InteliProjects/2023M4T7Inteli-grupo2/document/outros/imagens/cincoforcas2 (1).png

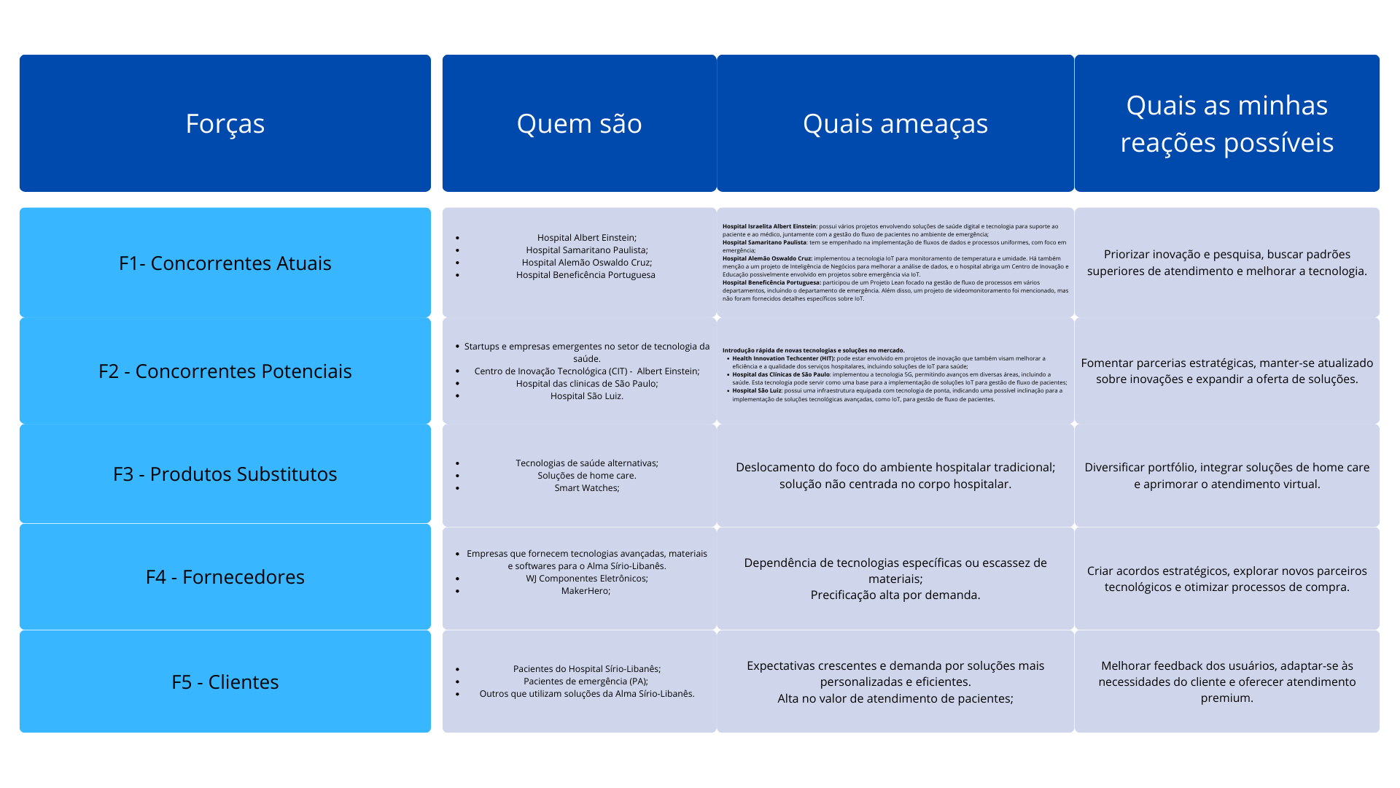
document/outros/imagens/cincoforcas2 (1).png
