InteliProjects/2023M4T7Inteli-grupo2/document/outros/imagens/dashboard_final.png

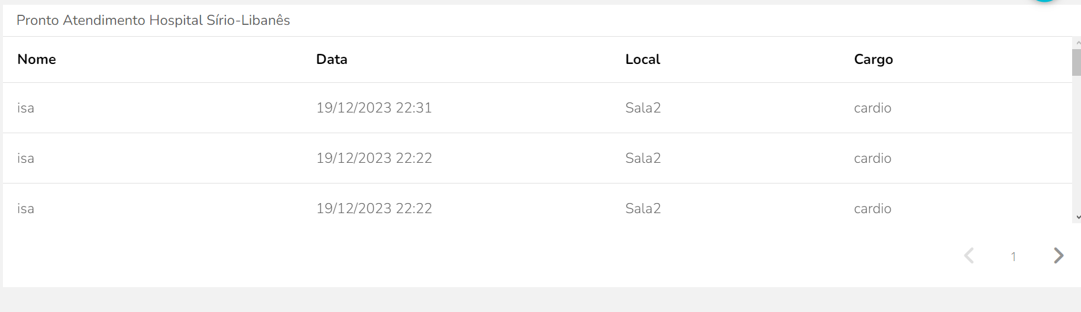
document/outros/imagens/dashboard_final.png
