InteliProjects/2023M4T7Inteli-grupo2/document/outros/imagens/Ubidots2.png

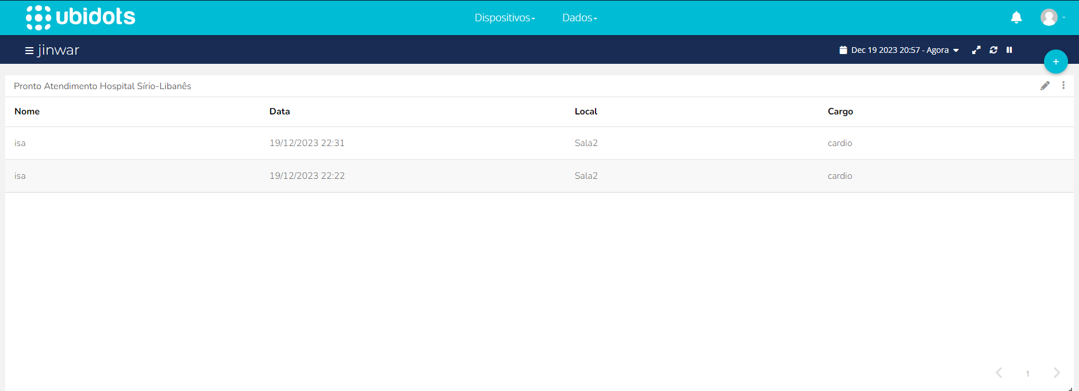
document/outros/imagens/Ubidots2.png
